kraemerlukas314/PinkyPi/images/IMG_20240503_134202.jpg

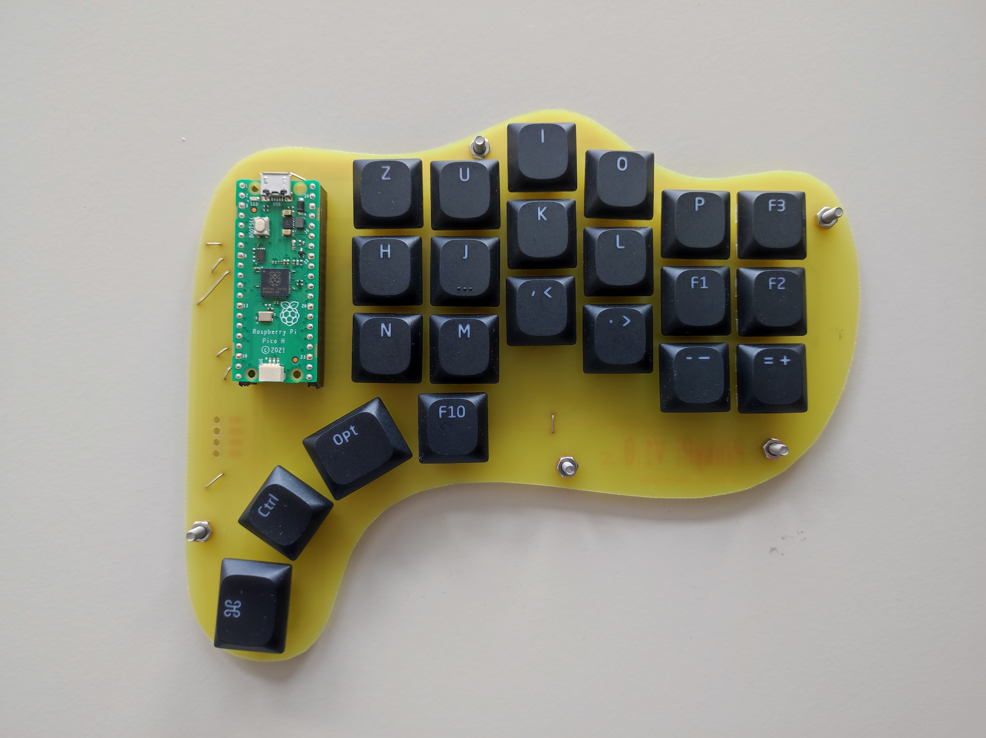
images/IMG_20240503_134202.jpg
