kraemerlukas314/PinkyPi/images/IMG_20240503_134219.jpg

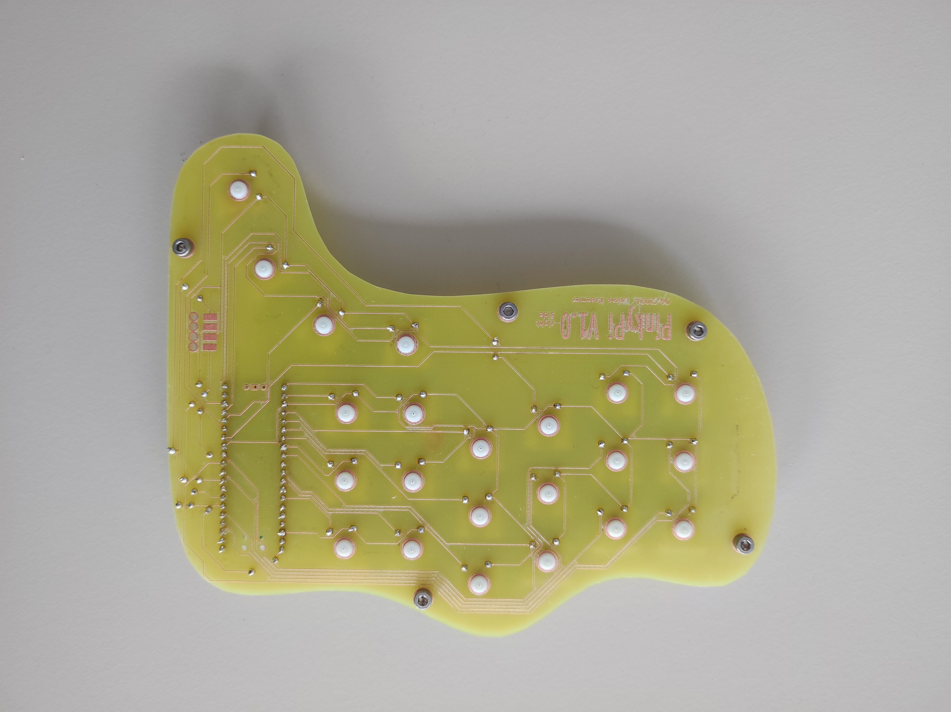
images/IMG_20240503_134219.jpg
